mldytech/saalio-smart/images/device_front.jpeg

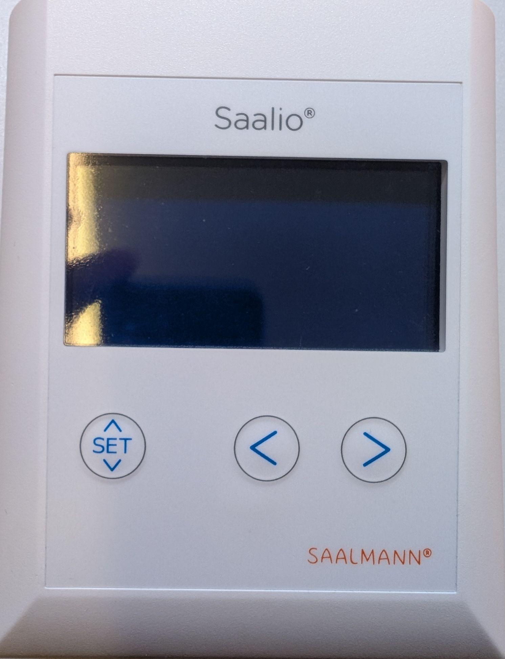
images/device_front.jpeg
